jsr606/EUROPROTO/SoundDays_MPlab/eagle/CFO EUROPROTO1 arduino nano/CFO EUROPROTO1 arduino nano.png

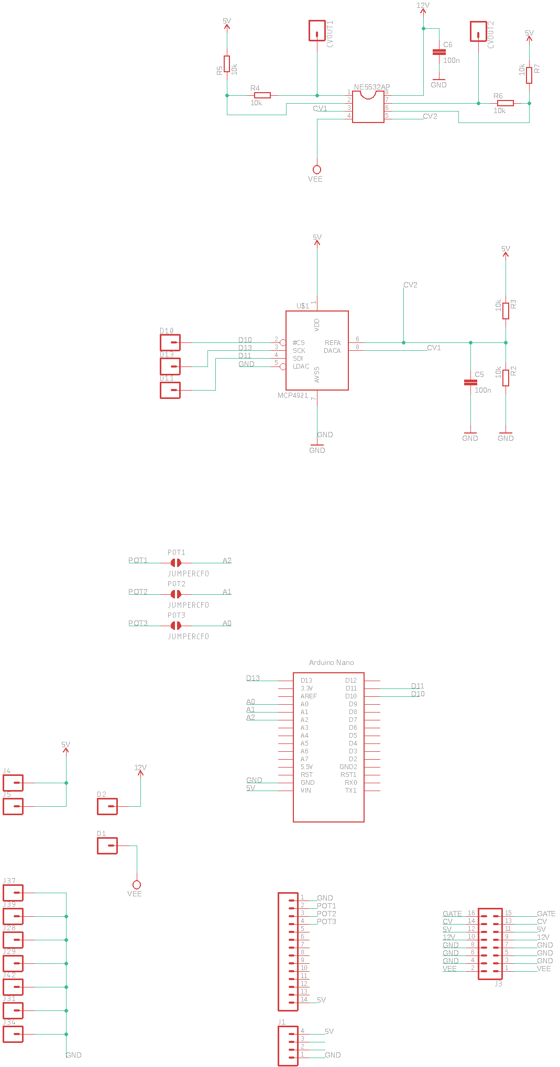
SoundDays_MPlab/eagle/CFO EUROPROTO1 arduino nano/CFO EUROPROTO1 arduino nano.png
