jsr606/EUROPROTO/SoundDays_MPlab/eagle/CFO EUROPROTO1 atmega328/EUROPROTO1_atmega328_mcp4921.png

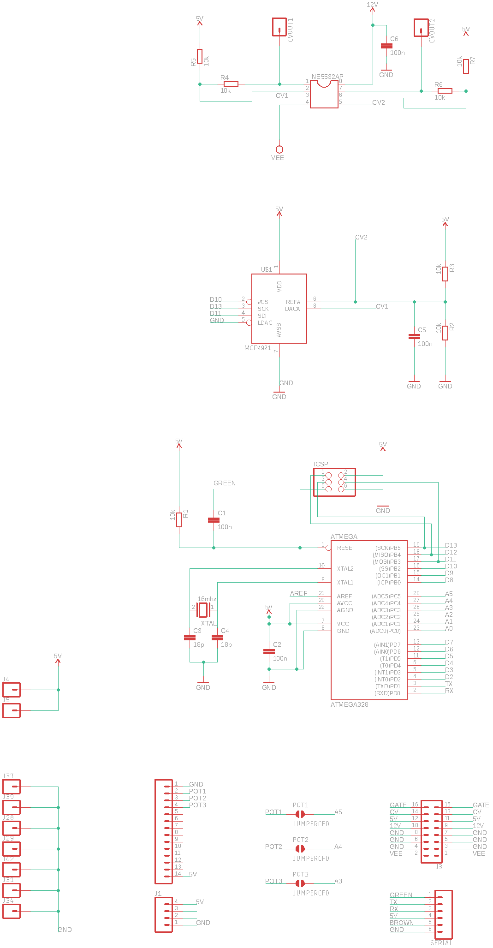
SoundDays_MPlab/eagle/CFO EUROPROTO1 atmega328/EUROPROTO1_atmega328_mcp4921.png
