jsr606/EUROPROTO/SoundDays_MPlab/code/arduino/pecussiveOscillator_CVtoGain/Wavetable.ino

/*********************************************
   Plays Sine Tone on Arduino Pocket Piano
   Author: Owen Osborn, Copyright: GPL

    This uses Direct Digital Synthesis (DDS) for tone generation

   5 October 2007

   FOR MCP4921 DAC

   Chip type           : ATMEGA168
   Clock frequency     : 16MHz
 *********************************************/
/* hacked up with lots of wavetables in progmem by Josh Brandt, 6 October 2008 */


#define SPI_SCK 5
#define SPI_MOSI 3


const uint8_t waveTable[] PROGMEM = {
  // sine
  0x80, 0x83, 0x86, 0x89, 0x8c, 0x8f, 0x92, 0x95, 0x98, 0x9c, 0x9f, 0xa2, 0xa5, 0xa8, 0xab, 0xae,
  0xb0, 0xb3, 0xb6, 0xb9, 0xbc, 0xbf, 0xc1, 0xc4, 0xc7, 0xc9, 0xcc, 0xce, 0xd1, 0xd3, 0xd5, 0xd8,
  0xda, 0xdc, 0xde, 0xe0, 0xe2, 0xe4, 0xe6, 0xe8, 0xea, 0xec, 0xed, 0xef, 0xf0, 0xf2, 0xf3, 0xf5,
  0xf6, 0xf7, 0xf8, 0xf9, 0xfa, 0xfb, 0xfc, 0xfc, 0xfd, 0xfe, 0xfe, 0xff, 0xff, 0xff, 0xff, 0xff,
  0xff, 0xff, 0xff, 0xff, 0xff, 0xff, 0xfe, 0xfe, 0xfd, 0xfc, 0xfc, 0xfb, 0xfa, 0xf9, 0xf8, 0xf7,
  0xf6, 0xf5, 0xf3, 0xf2, 0xf0, 0xef, 0xed, 0xec, 0xea, 0xe8, 0xe6, 0xe4, 0xe2, 0xe0, 0xde, 0xdc,
  0xda, 0xd8, 0xd5, 0xd3, 0xd1, 0xce, 0xcc, 0xc9, 0xc7, 0xc4, 0xc1, 0xbf, 0xbc, 0xb9, 0xb6, 0xb3,
  0xb0, 0xae, 0xab, 0xa8, 0xa5, 0xa2, 0x9f, 0x9c, 0x98, 0x95, 0x92, 0x8f, 0x8c, 0x89, 0x86, 0x83,
  0x80, 0x7c, 0x79, 0x76, 0x73, 0x70, 0x6d, 0x6a, 0x67, 0x63, 0x60, 0x5d, 0x5a, 0x57, 0x54, 0x51,
  0x4f, 0x4c, 0x49, 0x46, 0x43, 0x40, 0x3e, 0x3b, 0x38, 0x36, 0x33, 0x31, 0x2e, 0x2c, 0x2a, 0x27,
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
int16_t modulatorSigned;
uint16_t modulator;
uint16_t modDepth;
*/

uint32_t sample;     // final sample that goes to the DAC    

// variables for oscillator with no modulation
uint16_t accumulator = 0;
uint8_t index = 0;
uint32_t oscil= 0;
uint16_t oscil1 = 0;
uint16_t oscil2 = 0;

// variables for carrier oscillator
uint16_t phaseAccumCarrier;
uint16_t phaseDeltaCarrier;
uint8_t indexCarrier;
uint8_t carrier;
uint8_t carrierAmp;

// variables for frequency mod oscillator
uint16_t phaseAccumModulator;
uint16_t phaseDeltaModulator;
uint8_t indexModulator;
int16_t modulatorSigned;
uint16_t modulator;
uint16_t modDepth;


// the two bytes that go to the DAC over SPI
uint8_t dacSPI0;
uint8_t dacSPI1;

// timer 2 is audio interrupt timer
ISR(TIMER2_COMPA_vect) {
  OCR2A = 127;

  PORTB &= ~(1 << 2); // Frame sync low for SPI (making it low here so that we can measure lenght of interrupt with scope)

  phaseDeltaModulator = (frequency * harmonicity) >> 6;   // calculate modulator frequency for a given harmonicity
  phaseDeltaCarrier = frequency;                          // this is just pitch (although not in Hz)

  // calculate frequency mod
  phaseAccumModulator = phaseAccumModulator + phaseDeltaModulator;
  indexModulator = phaseAccumModulator >> 8;
  //  modulator = sineTable[indexModulator];

  memcpy_P(&modulator, &waveTable[modulatorWaveForm * 256 + indexModulator], 1);
  modulator = (modulator * modulatorDepth) >> 3;
  modulatorSigned = modulator - ((128 * modulatorDepth) >> 3);   // center at 0

  // get carrier frequency
  phaseDeltaCarrier += modulatorSigned;

  // calculate carrier
  phaseAccumCarrier = phaseAccumCarrier + (phaseDeltaCarrier);
  indexCarrier = phaseAccumCarrier >> 8;
  //  carrier = sineTable[indexCarrier];

  memcpy_P(&carrier, &waveTable[waveForm * 256 + indexCarrier], 1);


  sample = carrier * gain;

  // format sample for SPI port
  dacSPI0 = sample >> 8;
  dacSPI0 >>= 4;
  dacSPI0 |= 0x30;
  dacSPI1 = sample >> 4;

  //Serial.print("M = ");
  //Serial.println(SPCR & (1 << MSTR), DEC);

  SPCR |= (1 << MSTR);

  //Serial.print("m = ");
  //Serial.println(SPCR & (1 << MSTR), DEC);


  // transmit value out the SPI port
  SPDR = dacSPI0;
  while (!(SPSR & (1 << SPIF)));
  SPDR = dacSPI1;
  while (!(SPSR & (1 << SPIF)));
  PORTB |= (1 << 2); // Frame sync high
  
}
